JordanAceto/horrible_distortion/hardware/offboard_wiring/kicad_docs/bit_crusher_offboard_wiring.sch

## KiCad design hardware/offboard_wiring/kicad_docs/bit_crusher_offboard_wiring.sch (2020-11-16)

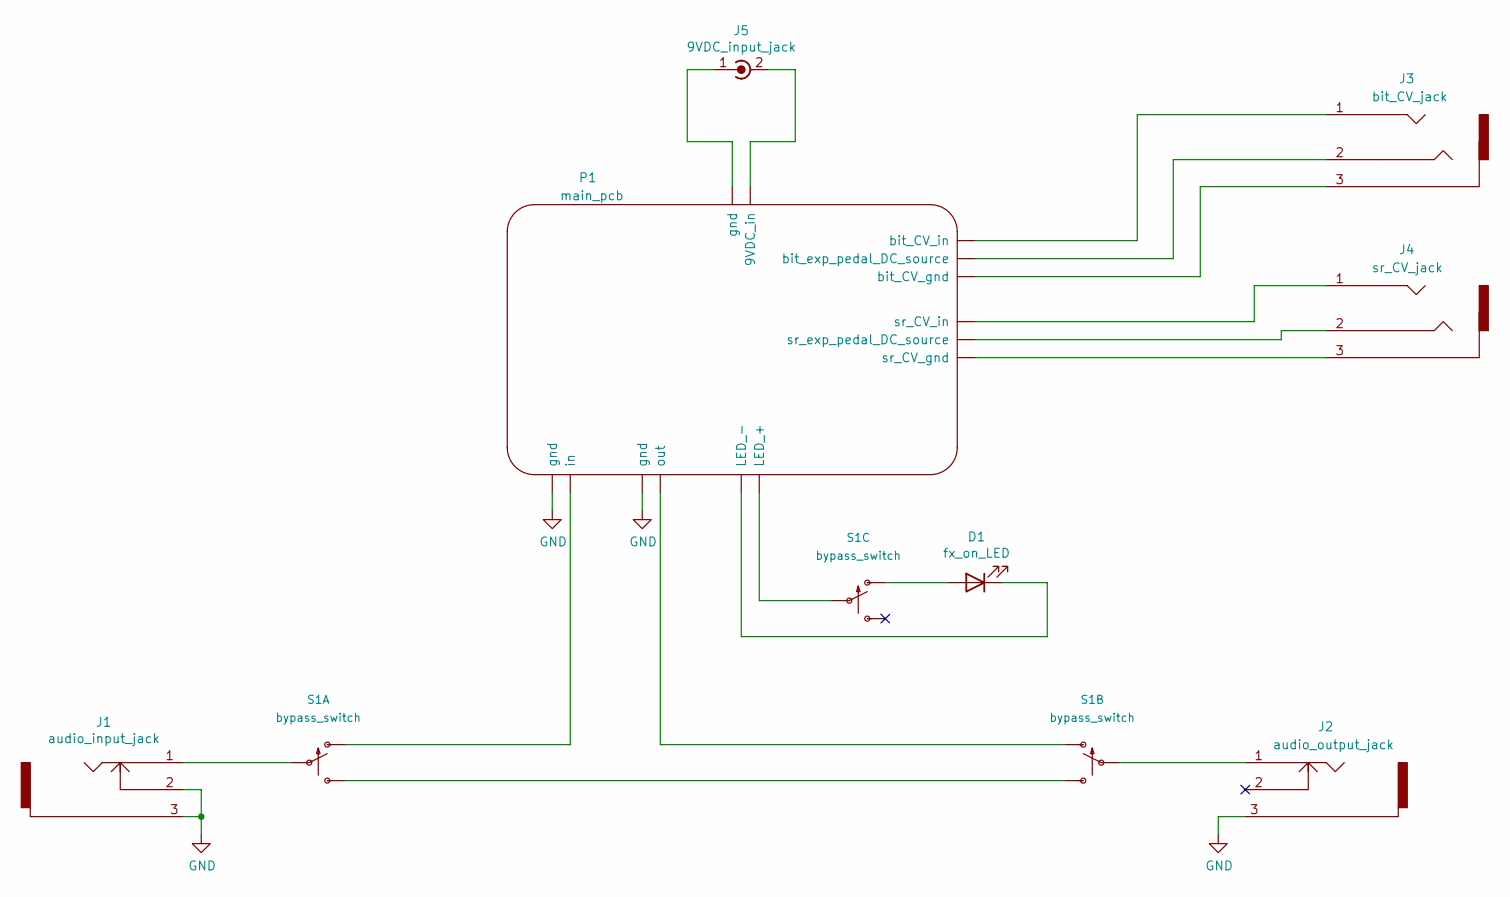
[picture p29: schematic bit_crusher_offboard_wiring.sch]

Parts:
D1: fx_on_LED
J1: audio_input_jack
J2: audio_output_jack
J3: bit_CV_jack
J4: sr_CV_jack
J5: 9VDC_input_jack
P1: main_pcb
S1: bypass_switch; STOMP_SWITCH_3PDT

Connections:
GND: J1.2, J1.3, J2.3, P1.~
unnamed: D1.1 (K), P1.~
unnamed: D1.2 (A), S1.P$7 (O)
unnamed: J1.1, S1.P$2
unnamed: J2.1, S1.P$5
unnamed: J3.1, P1.~
unnamed: J3.2, P1.~
unnamed: J3.3, P1.~
unnamed: J4.1, P1.~
unnamed: J4.2, P1.~
unnamed: J4.3, P1.~
unnamed: J5.1 (In), P1.~
unnamed: J5.2 (Ext), P1.~
unnamed: P1.~, S1.P$1 (O), S1.P$4 (O), S1.P$8
unnamed: S1.P$3 (S), S1.P$6 (S)
