JordanAceto/horrible_distortion/firmware/BSP/interrupts.h

/*
--|----------------------------------------------------------------------------|
--| FILE DESCRIPTION:
--|   interrupts.h provides the interface for the interrupts used by the system.
--|   
--|
--|----------------------------------------------------------------------------|
--| REFERENCES:
--|
--|----------------------------------------------------------------------------|
*/

#ifndef INTERRUPTS_H_INCLUDED
#define INTERRUPTS_H_INCLUDED

/*
--|----------------------------------------------------------------------------|
--| INCLUDE FILES
--|----------------------------------------------------------------------------|
*/

#include <stdbool.h>

/*
--|----------------------------------------------------------------------------|
--| PUBLIC TYPES
--|----------------------------------------------------------------------------|
*/

/*
--| NAME: Interrupt_Flag_t
--| DESCRIPTION: Enumeration of the interrupt flags used by the system
*/
typedef enum Interrupt_Flag_Type
{
    INTERRUPT_FLAG_TIM3 = 0u,
    INTERRUPT_FLAG_TIM6,

    NUM_INTERRUPT_FLAG_TYPES
} Interrupt_Flag_t;

/*
--|----------------------------------------------------------------------------|
--| PUBLIC FUNCTION PROTOTYPES
--|----------------------------------------------------------------------------|
*/

/*------------------------------------------------------------------------------
Function Name:
    interrupts_Init

Function Description:
    Perform initialization of the interrupts used by the system.

Parameters:
    None

Returns:
    None

Assumptions/Limitations:
    Assumed that this will be called as part of system initialization.
------------------------------------------------------------------------------*/
void interrupts_Init(void);

/*------------------------------------------------------------------------------
Function Name:
    interrupt_get_flag

Function Description:
    Get the status of the specified interrupt flag and clear the flag if it 
    was set.

Parameters:
    flag: the flag to check

Returns:
    True if the given interrupt flag is set, else false.

Assumptions/Limitations:
    Assumed that the flag is a member of the Interrupt_Flag_t enumeration.
------------------------------------------------------------------------------*/
bool interrupt_get_flag(Interrupt_Flag_t flag);

#endif
